martin2250/EnvironmentalLogger/Software/menuFunction.h

/*
 * menuFunction.h
 *
 * Created: 05.04.2015 22:22:32
 *  Author: Martin
 */ 


#ifndef MENUFUNCTION_H_
#define MENUFUNCTION_H_

void LcdOff();
void menuSetTime();
void menuSetDate();


void menuSetInterval();
void menuSetTimeout();
void menuResetEEPROM();
void menuToggleLogging();

#endif /* MENUFUNCTION_H_ */
