martin2250/EnvironmentalLogger/Software/showStatus.h

/*
 * showStatus.h
 *
 * Created: 06.04.2015 00:02:04
 *  Author: Martin
 */ 


#ifndef SHOWSTATUS_H_
#define SHOWSTATUS_H_

void ShowStatus();
void StatusAddMeasurements();

#endif /* SHOWSTATUS_H_ */
